ednieuw/ESP32-C3-Clock-and-more/Pics/img9.jpg

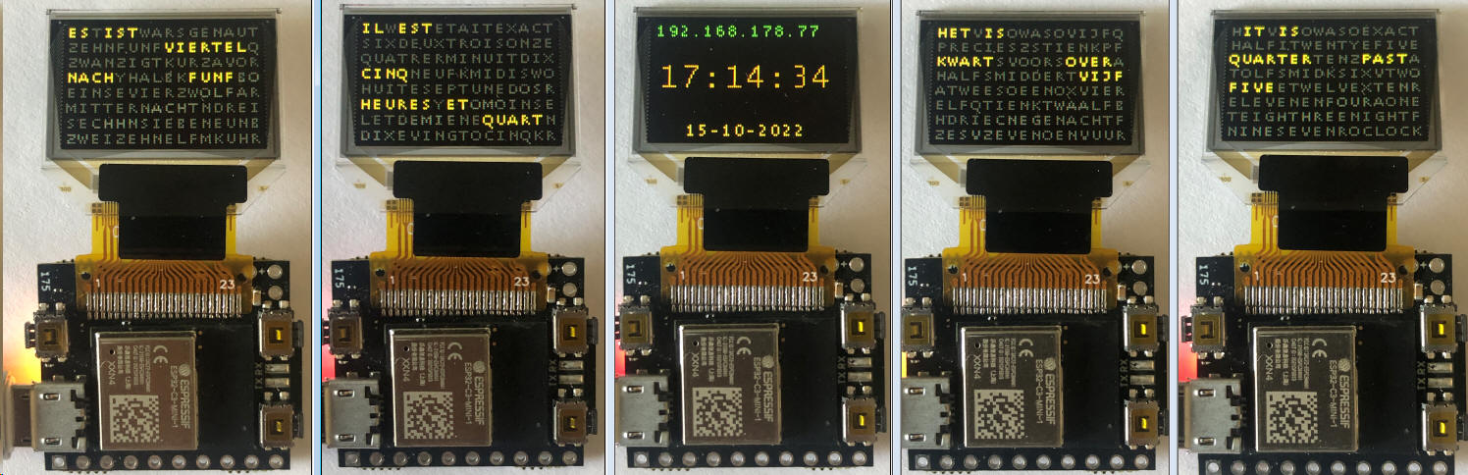
Pics/img9.jpg
