ednieuw/ESP32-C3-Clock-and-more/Pics/IMG_9451.JPG

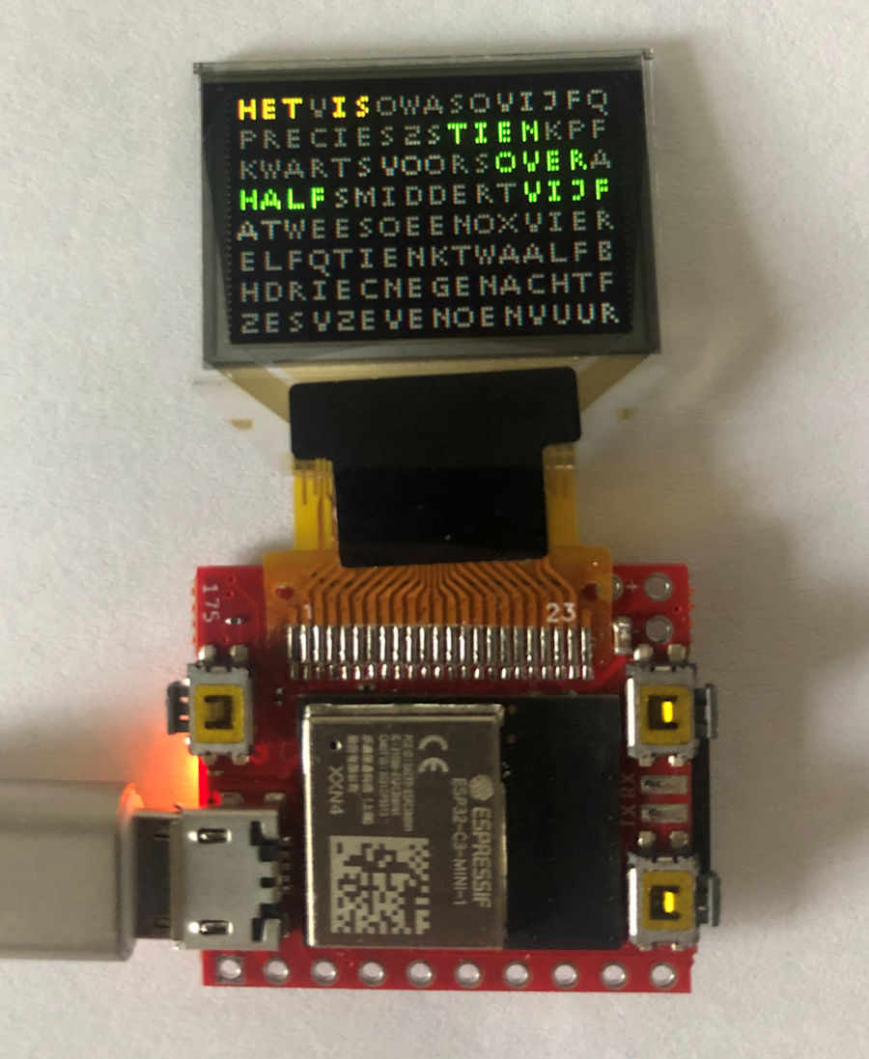
Pics/IMG_9451.JPG
