ednieuw/ESP32-C3-Clock-and-more/Pics/imgA.jpg

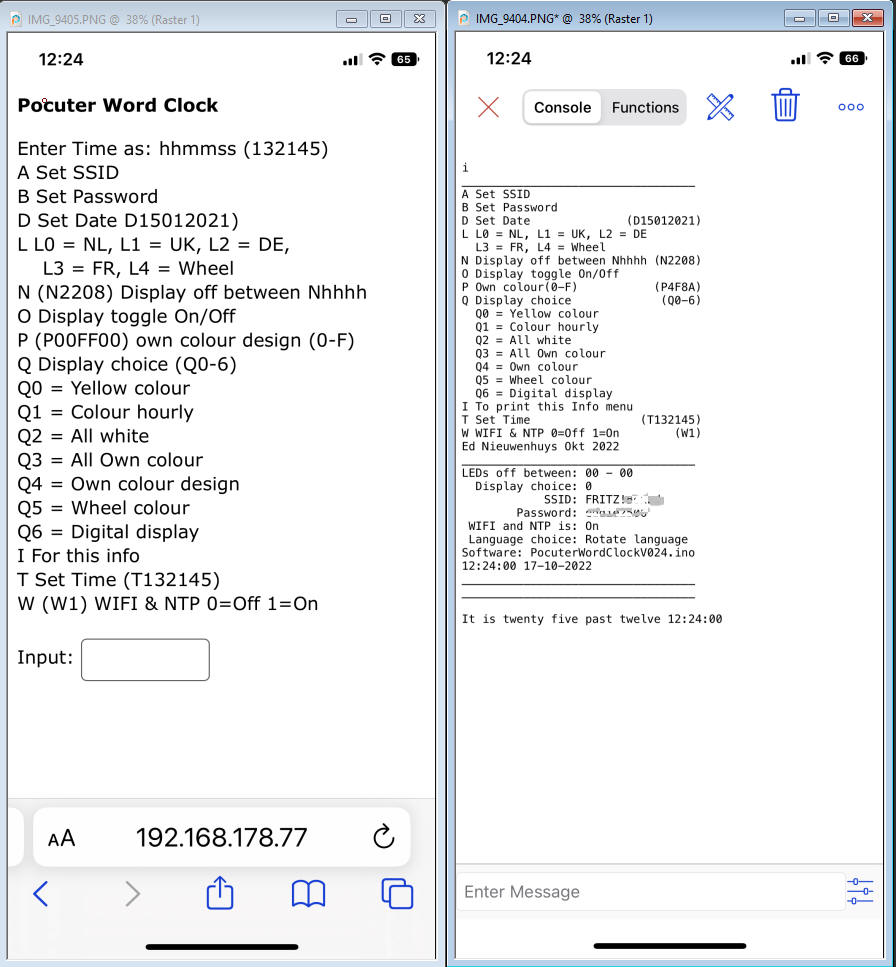
Pics/imgA.jpg
