ednieuw/ESP32-C3-Clock-and-more/Pics/MS_IP8.jpg

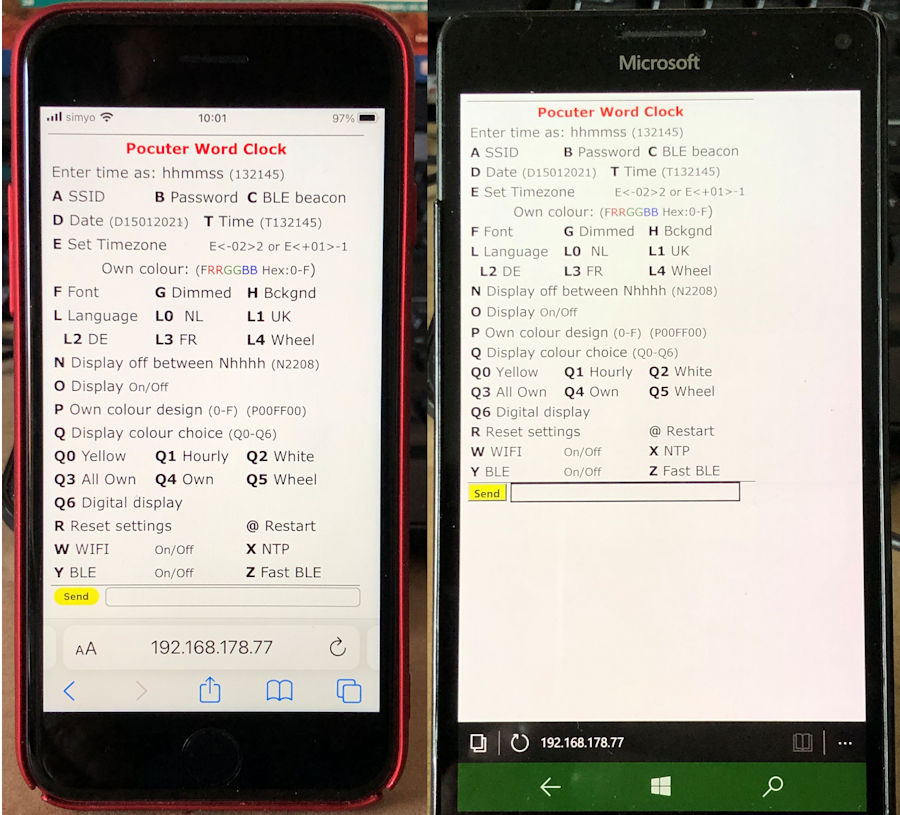
Pics/MS_IP8.jpg
